BLEhound/BLEhound/firmware/blehound/projects/blehound/src/host_iface.h

/* SPDX-License-Identifier: Apache-2.0 */
/*
 * Host interface —— sends captured packets to the host (Wireshark extcap) over USB CDC ACM.
 *
 * Wire format: each frame is first assembled per the structure below, then the whole thing is
 * COBS-encoded, with a single 0x00 delimiter appended at the end. The host only needs to split
 * on 0x00 and COBS-decode frame by frame; it re-aligns automatically if it joins mid-stream or
 * drops a byte.
 *
 * Capture frame (firmware → PC), little-endian:
 *
 *   Offset  Len  Field         Description
 *   ------  ---  ------------  --------------------------------------------
 *      0     1  type          HOST_FRAME_PACKET
 *      1     1  flags         see HOST_FLAG_*
 *      2     4  timestamp_us  time the access address was received (µs)
 *      6     1  channel       BLE channel index 0..39
 *      7     1  rssi          int8, dBm (negative)
 *      8     1  phy           0=1M 1=2M 2=Coded S8 3=Coded S2
 *      9     4  access_addr   0x8E89BED6 for advertising, the connection's AA otherwise
 *     13     3  crc           the received 24-bit CRC, raw
 *     16     1  pdu_len       number of PDU bytes that follow (= 2 + payload length)
 *     17     N  pdu           complete LL PDU: header(1) + length(1) + payload
 *
 * The host concatenates access_addr + pdu + crc in that order to form the link-layer frame
 * that Wireshark's LINKTYPE_BLUETOOTH_LE_LL_WITH_PHDR expects.
 *
 * Command frame (PC → firmware), also COBS-framed:
 *
 *   Offset  Len  Field         Description
 *   ------  ---  ------------  --------------------------------------------
 *      0     1  type          HOST_CMD_*
 *      1     N  args          command-specific
 */

#ifndef HOST_IFACE_H_
#define HOST_IFACE_H_

#include <stdbool.h>
#include <stdint.h>

#include "radio_hal.h"

/* ---- frame types ---- */
#define HOST_FRAME_PACKET     0x01   /**< capture frame, firmware → PC */
#define HOST_FRAME_STATUS     0x02   /**< status frame, firmware → PC (reply to HOST_CMD_QUERY_STATUS)
                                       *   little-endian, COBS framed, layout:
                                       *   off  len  field
                                       *    0    1   type = HOST_FRAME_STATUS
                                       *    1    1   status_version (currently 1)
                                       *    2    1   board_id 0/1/2
                                       *    3    1   guard_channel, the guarded advertising channel 37/38/39
                                       *    4    1   flags: bit0 single-target bit1 hopping bit2 target set
                                       *                    bit3 following a connection bit4 SYNC active bit5 IRK set
                                       *    5    4   sync_count (board 0 = SYNC edges emitted, boards 1/2 = captured)
                                       *    9    4   connects_seen, CONNECT_INDs captured
                                       *   13    1   active_now, connections currently followed
                                       *   14    1   fw_len, length N of the firmware version string
                                       *   15    N   firmware version string (ASCII, no terminating 0) */

#define HOST_FRAME_SYNC       0x03   /**< SYNC heartbeat, firmware → PC: sent proactively after every SYNC edge, regardless of
                                       *   whether packets were captured (in single-target mode non-target packets are all
                                       *   filtered, so capture frames may stop for seconds; a host that only took sync_epoch
                                       *   from capture frames got a stale tick, paired edges 1 s off, and every tri-board relay
                                       *   anchor was wrong). Layout (little-endian): 0 type=3; 1 board_id; 2..5 sync_count; 6..9 sync_epoch */

#define HOST_CMD_SET_CHANNEL  0x81   /**< arg: 1 byte, BLE channel index 0..39 */
#define HOST_CMD_START        0x82   /**< no args, start capturing */
#define HOST_CMD_STOP         0x83   /**< no args, stop capturing */
#define HOST_CMD_SET_TARGET   0x84   /**< arg: 6-byte MAC (little-endian); all-zero = clear filter */
#define HOST_CMD_SET_HOPPING  0x85   /**< arg: 1 byte, nonzero enables three-channel round-robin scan */
#define HOST_CMD_FOLLOW       0x86   /**< tri-device co-follow relay: the host hands the connection
                                       *   parameters captured by one device to the other two so they
                                       *   take over following. Args are 25 bytes (little-endian): aa(4)
                                       *   crc_init(3) chan_map(5) hop(1) csa2(1) interval(2) latency(2)
                                       *   timeout(2) win_size(1) anchor0_us(4). anchor0_us is the event0
                                       *   anchor in µs on **this device's** TIMER time base. */
#define HOST_CMD_SET_SINGLE_TARGET 0x87 /**< arg: 1 byte, nonzero = single-target mode (default on): with no target set,
                                          *   only scan advertising and follow no connection; with a target set, follow only
                                          *   that target's connection and stop scanning / accepting new ones once following;
                                          *   0 = multi-target evaluation mode, follow everything (up to 6) */
#define HOST_CMD_QUERY_STATUS 0x88   /**< no args, the firmware replies with one HOST_FRAME_STATUS frame */
#define HOST_CMD_LL_CTRL_HINT 0x8A   /**< Key hint: an encrypted LL control PDU of some connection that the host decrypted with the
                                       *   LTK and relays to the firmware. Args: access_addr (4, little-endian) + plaintext LL data
                                       *   PDU (2-byte header + payload, MIC stripped). The firmware treats it as a plaintext control
                                       *   packet received on that connection, so channel-map / connection-parameter / PHY updates
                                       *   switch at the instant as usual and the link is no longer lost after encryption. */
#define HOST_CMD_ENTER_DFU    0x8B   /**< no args, enter firmware update mode: the firmware writes the boot mode into the
                                       *   retained register and resets, MCUboot starts the firmware loader (re-enumerates on
                                       *   USB as "BLEhound Loader", PID 0x5210, SMP/mcumgr protocol). This serial port goes
                                       *   away, no reply is sent; after the loader has written the new image and reset, the
                                       *   app is back. Firmware built without DFU ignores the command. */
#define HOST_CMD_SET_IRK      0x89   /**< arg: 16-byte IRK in **over-the-air / SMP Identity Information order (LSO first)**,
                                       *   matching the device log line "IRK wire/LSO-first"; all zero = clear. With an IRK set,
                                       *   the firmware uses ah() to recognise the target's new RPAs and makes them the current
                                       *   target MAC automatically, so a privacy device is not lost when it changes address.
                                       *   HOST_CMD_SET_TARGET with all zeros clears the IRK as well. */

/* ---- STATUS flags bits ---- */
#define HOST_STATUS_SINGLE_TARGET (1U << 0)
#define HOST_STATUS_HOPPING       (1U << 1)
#define HOST_STATUS_TARGET_SET    (1U << 2)
#define HOST_STATUS_FOLLOWING     (1U << 3)
#define HOST_STATUS_SYNC_ACTIVE   (1U << 4)
#define HOST_STATUS_IRK_SET       (1U << 5)

/** Status snapshot, filled in by main and handed to host_iface_send_status for encoding and upload. */
struct host_status {
	uint8_t     board_id;
	uint8_t     guard_channel;
	uint8_t     flags;          /**< OR of HOST_STATUS_* bits */
	uint32_t    sync_count;
	uint32_t    connects_seen;
	uint8_t     active_now;
	const char *fw_version;     /**< ASCII version string, NULL counts as empty */
};

/* ---- flags bits ---- */
#define HOST_FLAG_CRC_OK      (1U << 0)  /**< CRC check passed */
#define HOST_FLAG_DIR_S2M     (1U << 1)  /**< direction peripheral→central (meaningful only when HOST_FLAG_DIR_KNOWN is set) */
#define HOST_FLAG_ENCRYPTED   (1U << 2)  /**< this packet is encrypted (reserved for phases B/C) */
#define HOST_FLAG_TRI         (1U << 3)  /**< tri-device mode: 5-byte extension after the header (board_id + sync_epoch) */
#define HOST_FLAG_DIR_KNOWN   (1U << 4)  /**< Direction of a data-channel packet is known: the follower decides by air timing within
                                            *   the connection event, first packet = central→peripheral, every packet one T_IFS later flips
                                            *   the direction (dir_policy.h); not set when a dropped packet makes it ambiguous */

/** header length (all fixed fields before pdu) */
#define HOST_FRAME_HEADER_LEN 17

/**
 * Tri-device extension length (present only when flags has HOST_FLAG_TRI, immediately after the fixed header):
 *   Offset (from hdr end)  Len   Field
 *   ------------------  ----  ------------------------------------------
 *      0                 1    board_id     this board's id 0/1/2 (design doc §4.5)
 *      1                 4    sync_epoch   this board's TIMER tick at the most recent SYNC edge (µs, little-endian; 0 = none yet)
 * Older boards do not set HOST_FLAG_TRI and pdu still sits at offset HOST_FRAME_HEADER_LEN —— backward compatible.
 */
#define HOST_TRI_EXT_LEN      5

/** Callback invoked when a command is received. Called in CDC interrupt context, so keep it short. */
typedef void (*host_cmd_cb_t)(uint8_t cmd, const uint8_t *args, uint8_t args_len);

/**
 * Initialize CDC ACM and register the command callback.
 *
 * @return 0 on success, negative errno on failure
 */
int host_iface_init(host_cmd_cb_t cmd_cb);

/**
 * Whether the host has opened the serial port (DTR asserted). While it is not open, sends are
 * dropped outright to avoid filling up the TX buffer.
 */
bool host_iface_connected(void);

/**
 * Send one capture frame. Non-blocking: if there is not enough buffer space it drops the frame and
 * counts it, never blocking the caller.
 *
 * @return 0 queued for transmission, -ENOTCONN host not connected, -ENOMEM buffer full (counted)
 */
int host_iface_send_packet(const struct radio_packet *pkt, uint32_t access_addr,
			   uint8_t phy);

/**
 * Send a capture frame with tri-device metadata (HOST_FLAG_TRI): additionally carries board_id and
 * sync_epoch, so the host can tag the source board when merging three streams and align timestamps
 * onto a common time base. Otherwise identical to host_iface_send_packet.
 *
 * @param board_id     this board's id 0/1/2
 * @param sync_epoch   this board's TIMER-time-base tick at the most recent SYNC edge (0 = none yet)
 * @return same as host_iface_send_packet
 */
int host_iface_send_packet_tri(const struct radio_packet *pkt, uint32_t access_addr,
			       uint8_t phy, uint8_t board_id, uint32_t sync_epoch,
			       uint8_t direction);
/** direction values: 0 unknown, 1 central→peripheral, 2 peripheral→central (HOST_DIR_*) */
#define HOST_DIR_UNKNOWN 0
#define HOST_DIR_C2P     1
#define HOST_DIR_P2C     2

/**
 * Send one status frame (HOST_FRAME_STATUS). It shares the TX ring buffer with capture frames,
 * so it must be called from the **capture dequeue thread** (the only producer), never directly
 * from the CDC command interrupt.
 *
 * @return same as host_iface_send_packet
 */
int host_iface_send_status(const struct host_status *st);

/**
 * Send one SYNC heartbeat frame (HOST_FRAME_SYNC). Like the status frame, it may only be called from the capture dequeue thread.
 */
int host_iface_send_sync(uint8_t board_id, uint32_t sync_count, uint32_t sync_epoch);

/** Number of frames dropped due to insufficient TX buffer space */
uint32_t host_iface_dropped(void);

#endif /* HOST_IFACE_H_ */
